451bit/CO2-Ampel/Bilder/00.jpg

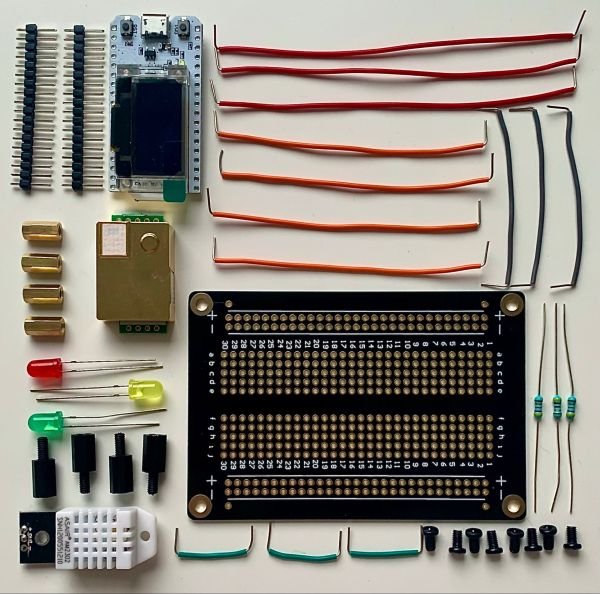
Bilder/00.jpg
