451bit/CO2-Ampel/Bilder/sm.jpg

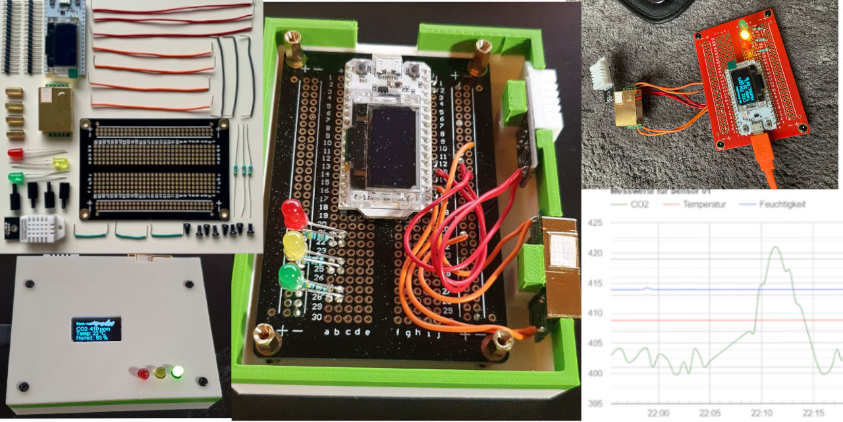
Bilder/sm.jpg
